neelshearer/beTheGoalie/GA/btg01.jpg

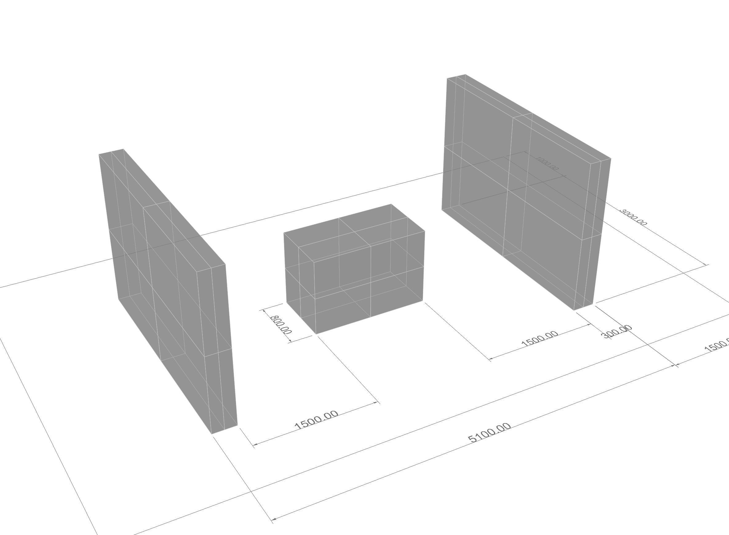
GA/btg01.jpg
