neelshearer/beTheGoalie/GA/btg02.jpg

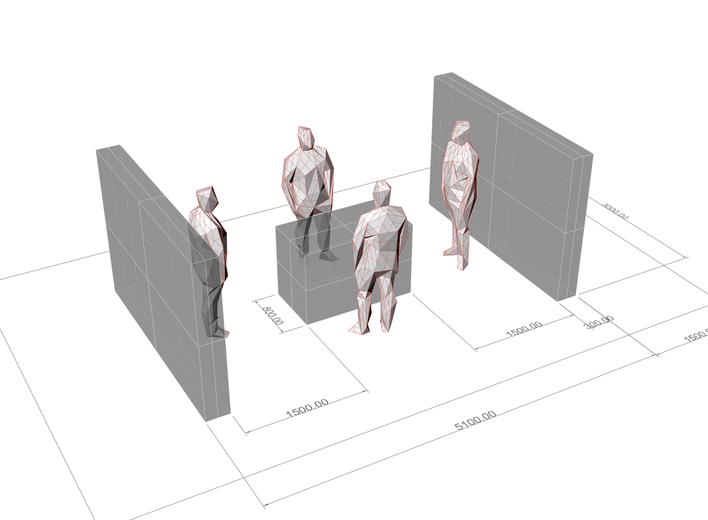
GA/btg02.jpg
