neelshearer/beTheGoalie/GA/btg03.jpg

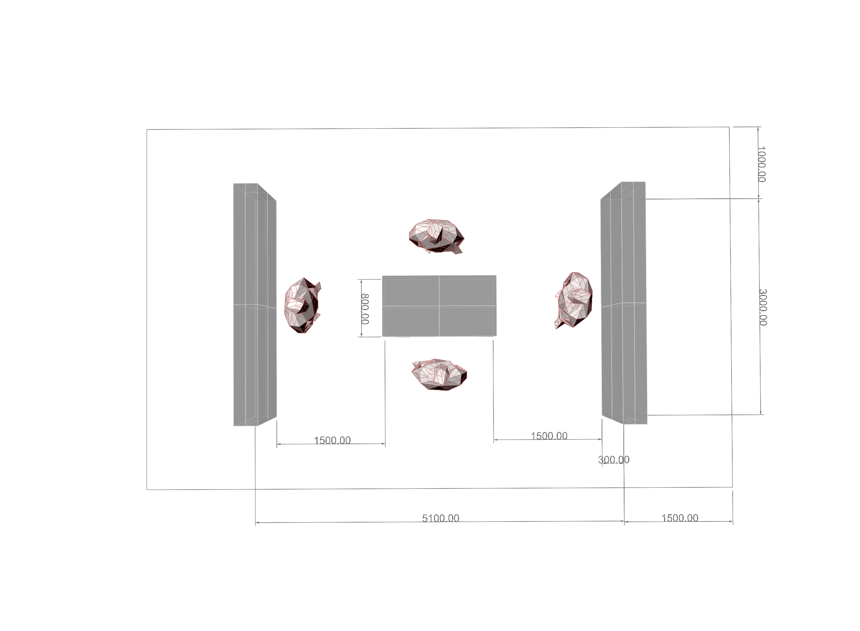
GA/btg03.jpg
