neelshearer/beTheGoalie/GA/btg04.jpg

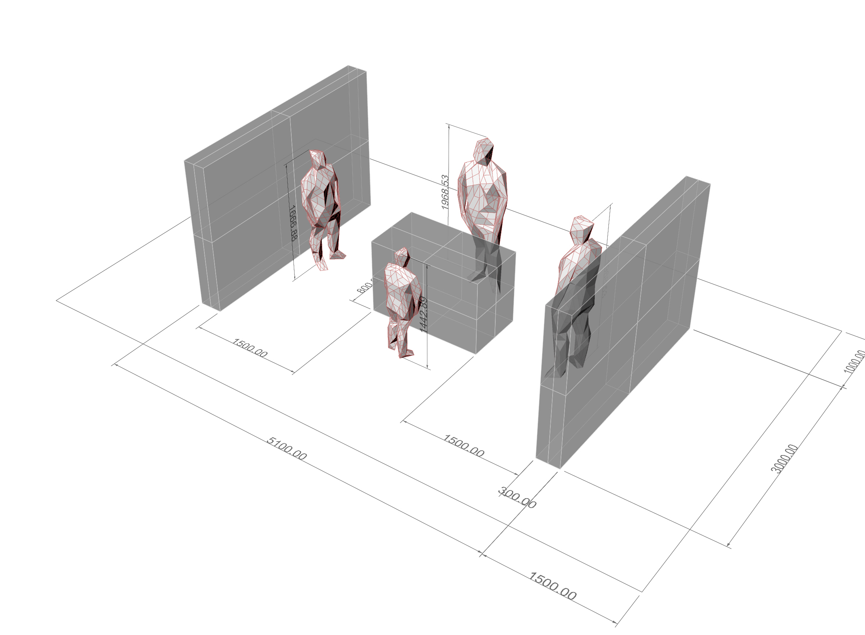
GA/btg04.jpg
