neelshearer/beTheGoalie/GA/btg06.jpg

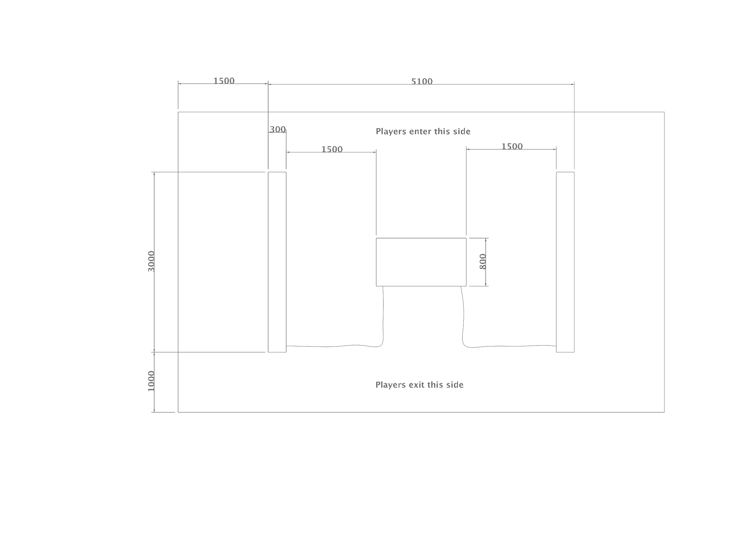
GA/btg06.jpg
