neelshearer/beTheGoalie/GA/btg07.jpg

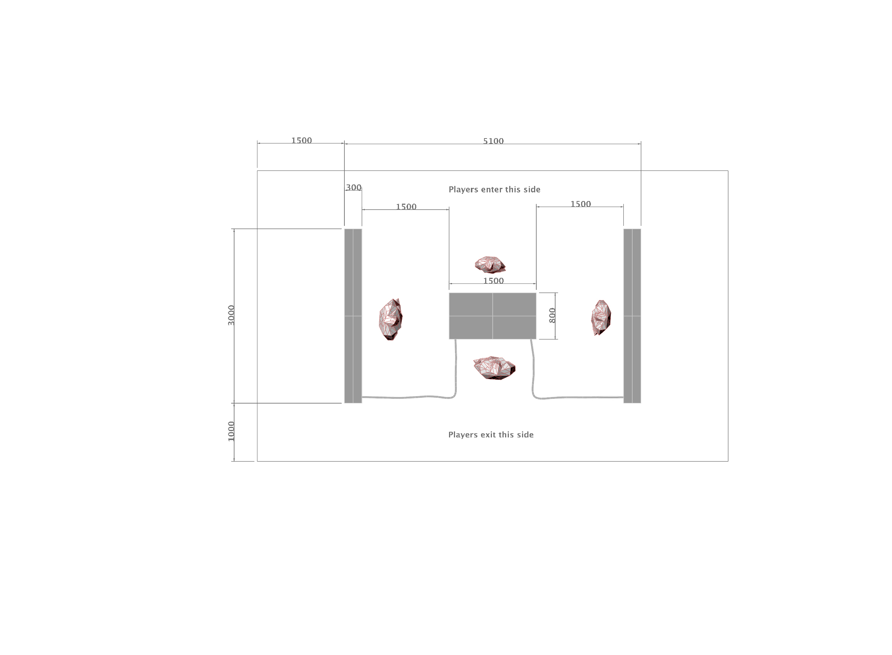
GA/btg07.jpg
