neelshearer/beTheGoalie/GA/btg10.jpg

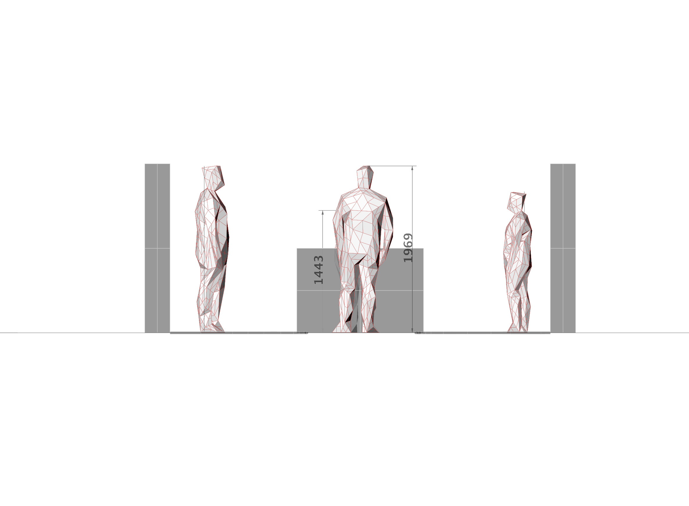
GA/btg10.jpg
