neelshearer/beTheGoalie/GA/btg12.jpg

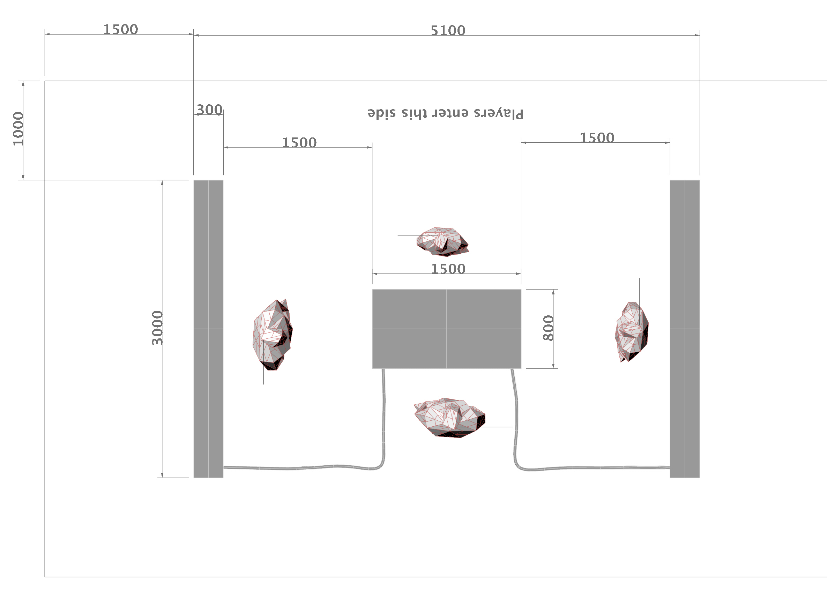
GA/btg12.jpg
