neelshearer/beTheGoalie/GA/btg13.jpg

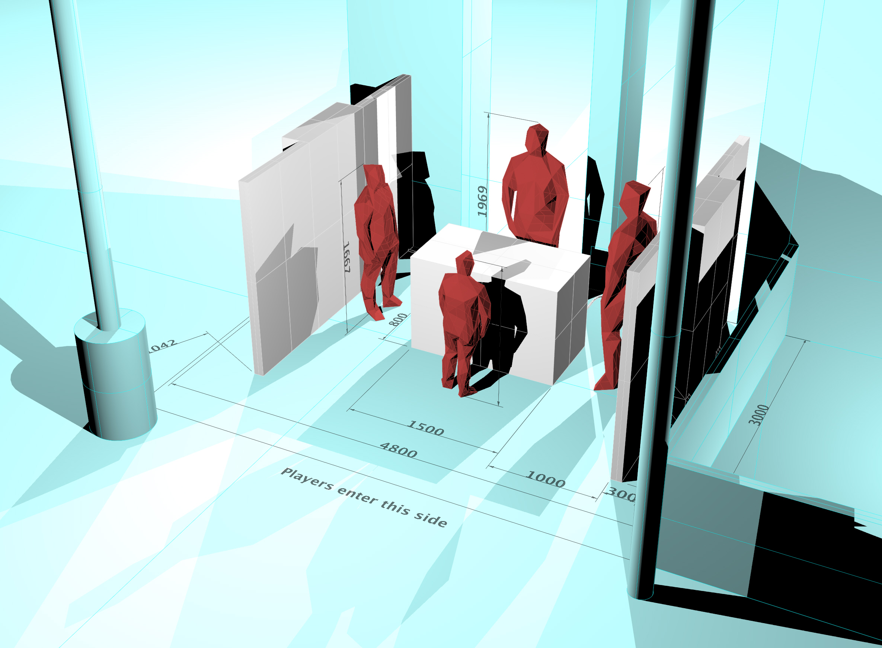
GA/btg13.jpg
