neelshearer/beTheGoalie/GA/my-friend-boris-1.snapshot.3/boris_lowpoly_160713.jpg

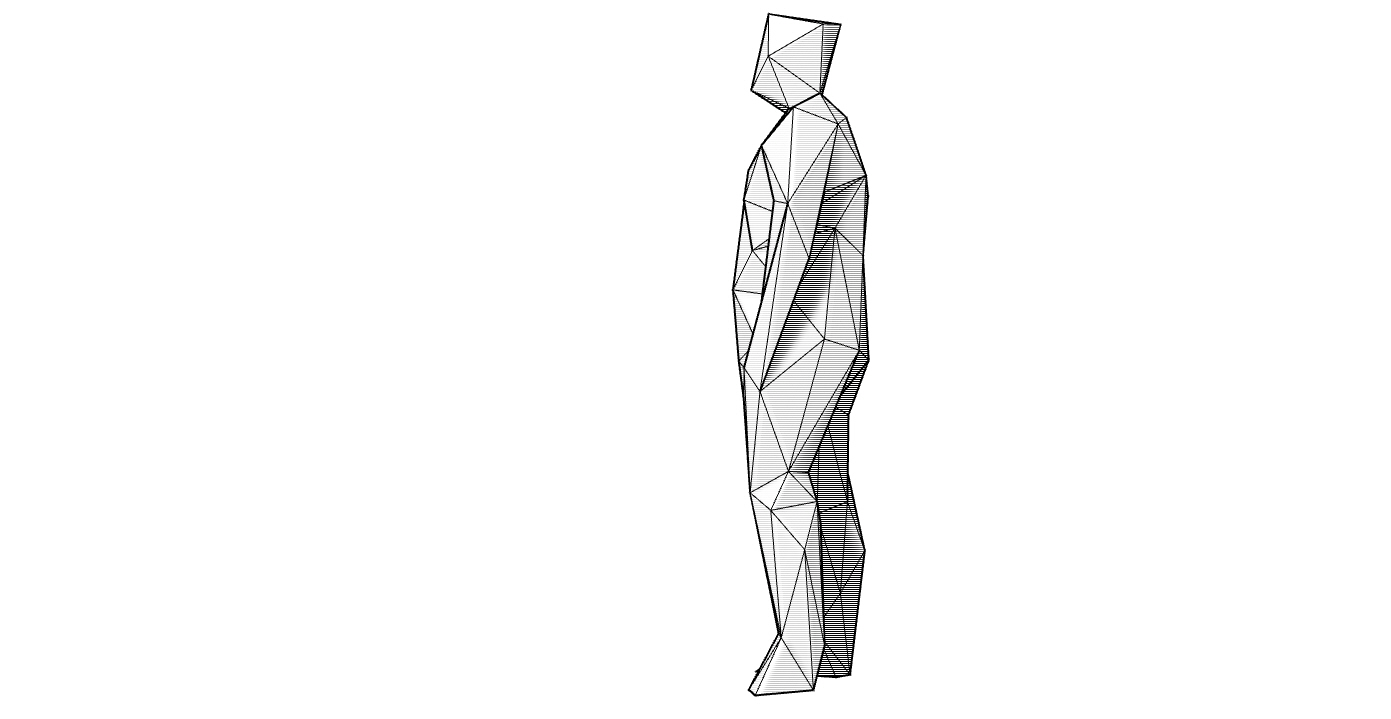
GA/my-friend-boris-1.snapshot.3/boris_lowpoly_160713.jpg
