neelshearer/beTheGoalie/Processing/BtG_mk25/data/photo4.jpg

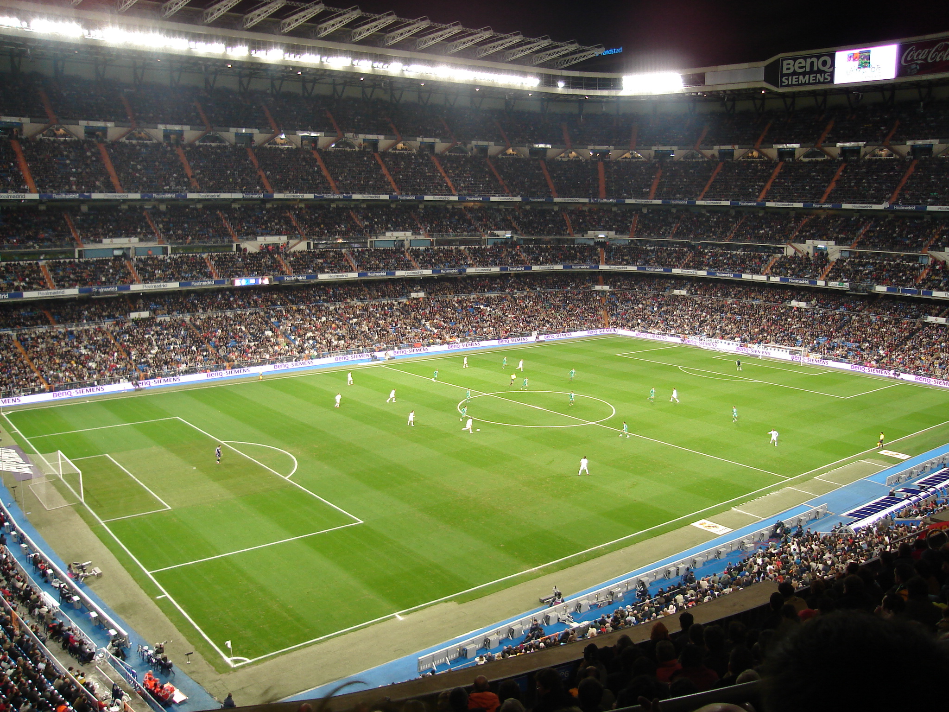
Processing/BtG_mk25/data/photo4.jpg
