neelshearer/beTheGoalie/wall structure mk2/Computer cavity and apertures.jpg

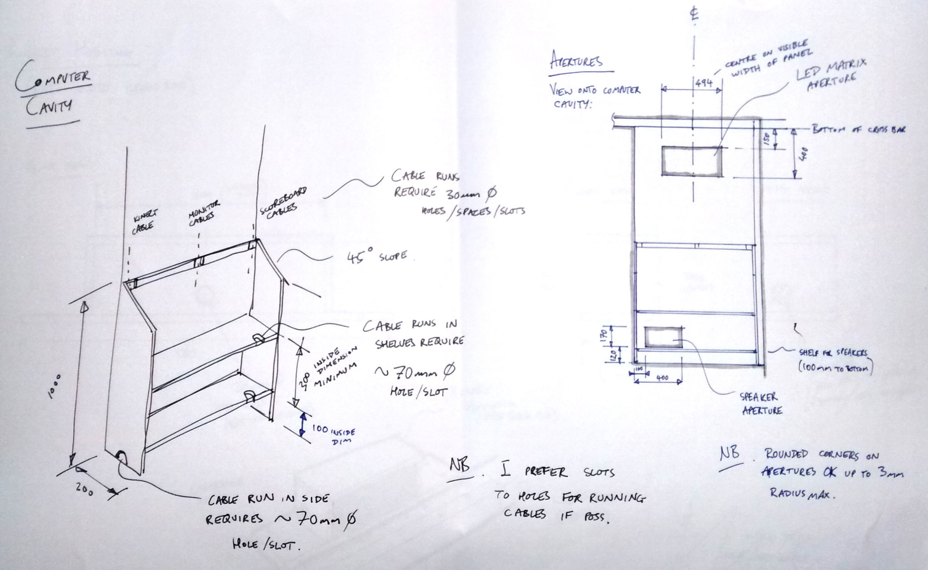
wall structure mk2/Computer cavity and apertures.jpg
