neelshearer/beTheGoalie/wall structure mk2/computer_cavity.jpg

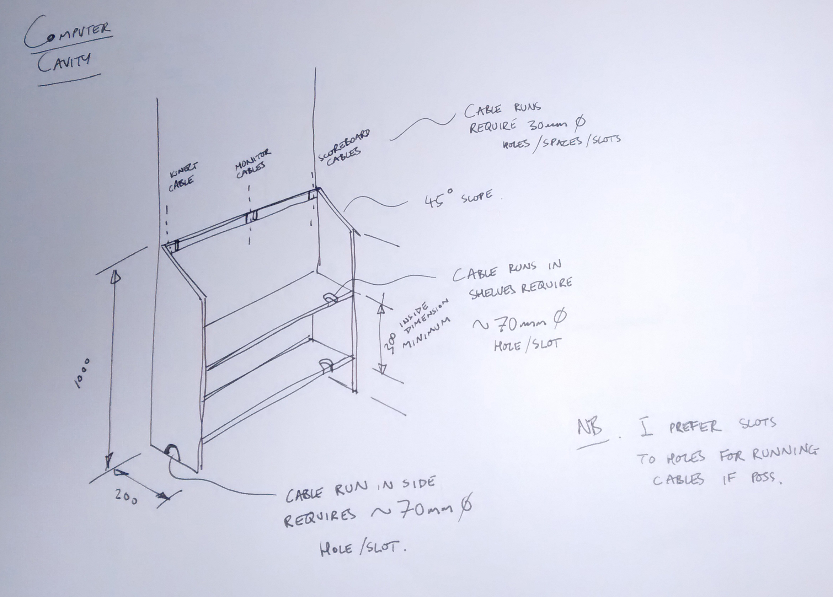
wall structure mk2/computer_cavity.jpg
