neelshearer/beTheGoalie/wall structure mk2/crossbar.jpg

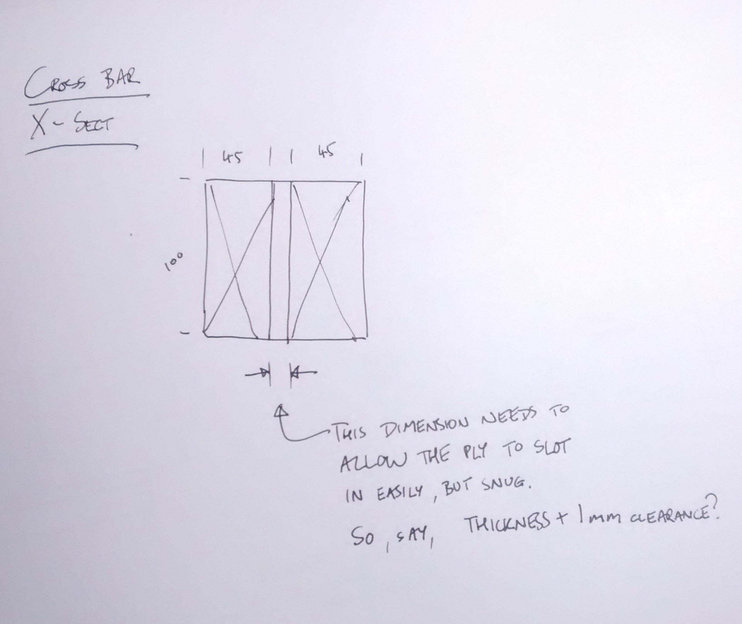
wall structure mk2/crossbar.jpg
