neelshearer/beTheGoalie/wall structure mk2/p1.jpg

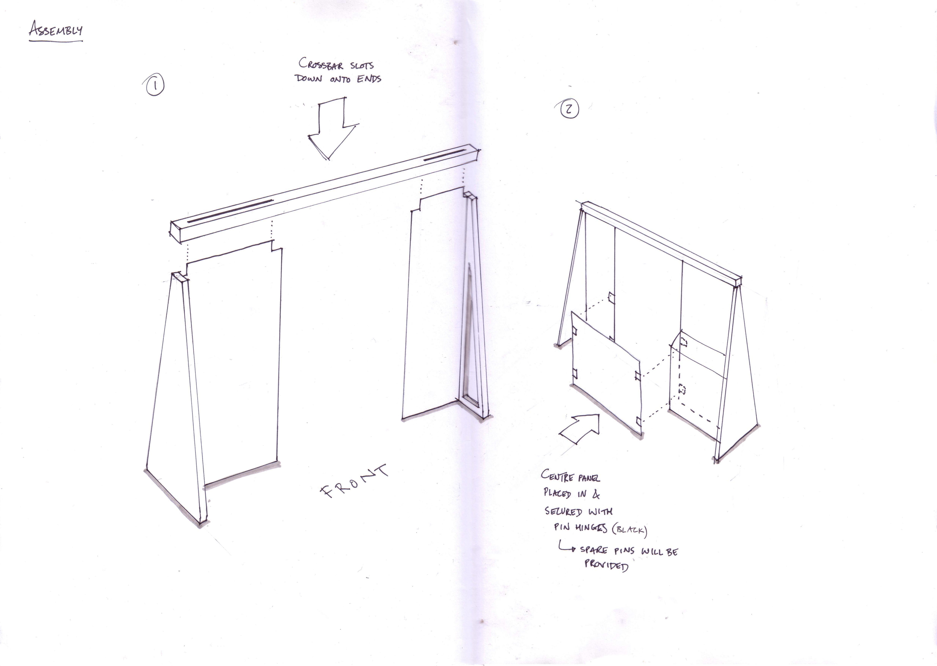
wall structure mk2/p1.jpg
