neelshearer/beTheGoalie/wall structure mk2/p2.jpg

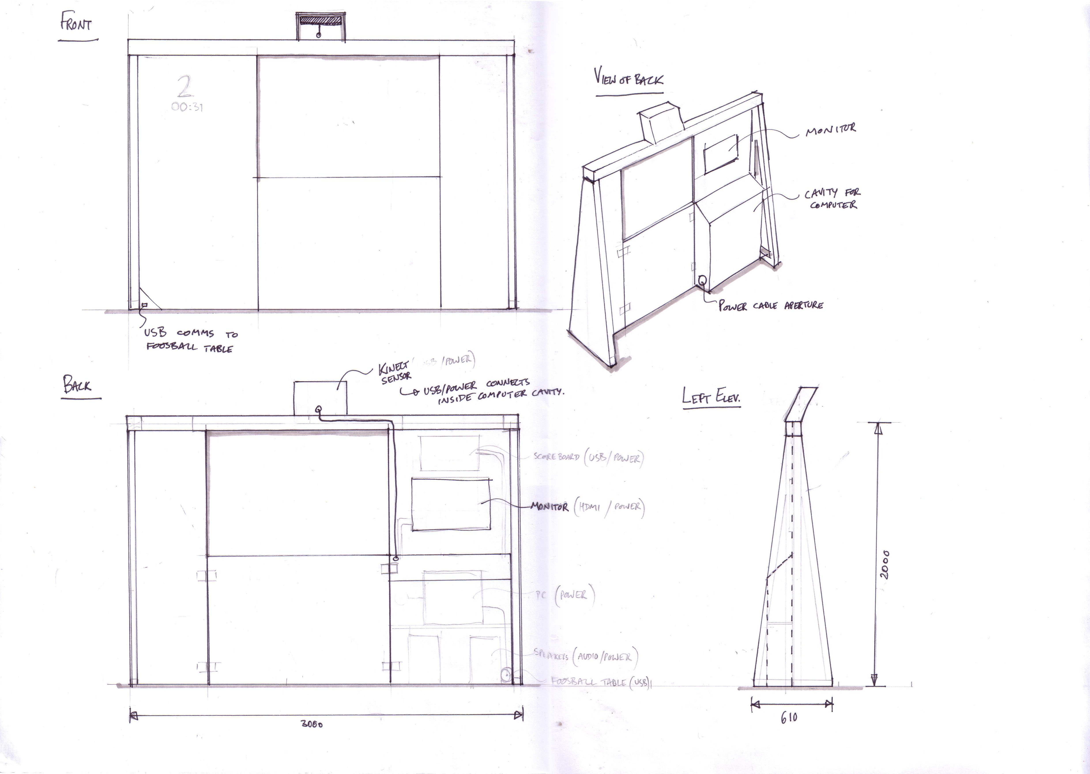
wall structure mk2/p2.jpg
