neelshearer/beTheGoalie/wall structure mk2/p3.jpg

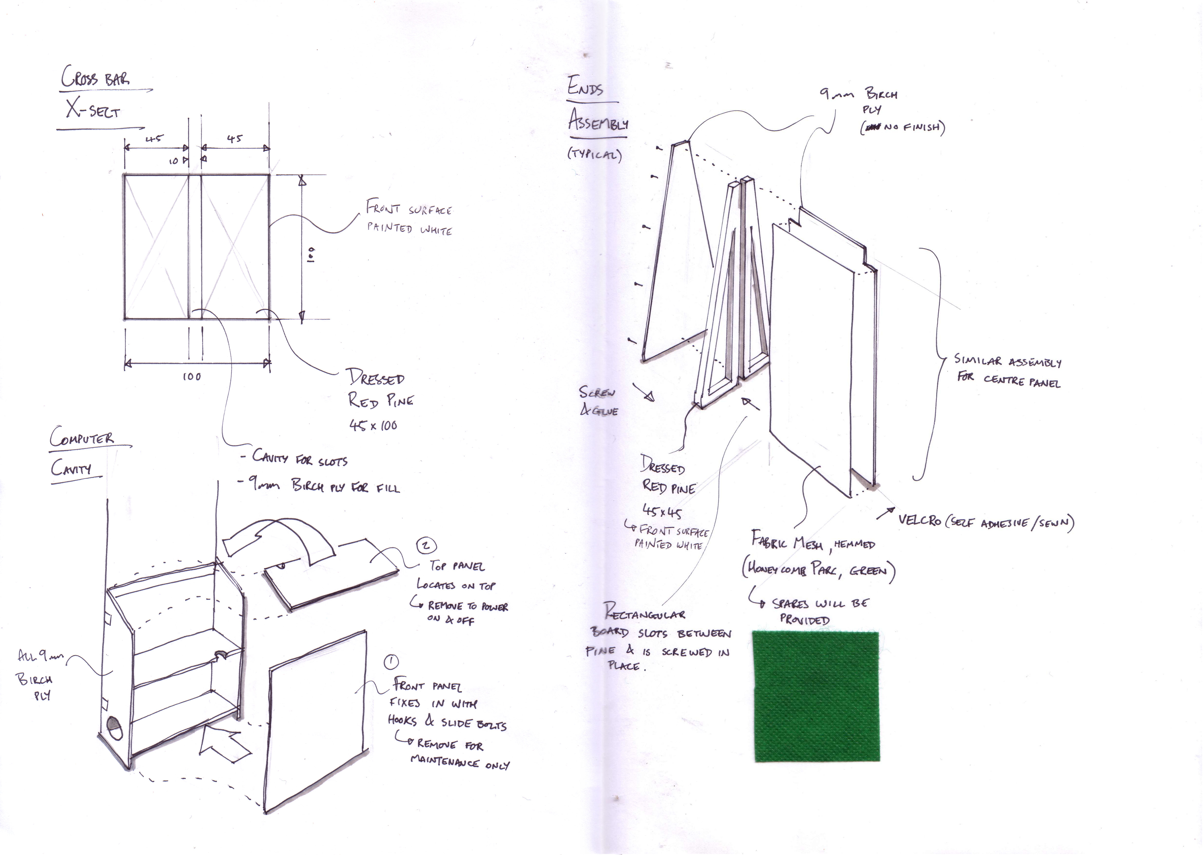
wall structure mk2/p3.jpg
