neelshearer/beTheGoalie/wall structure mk2/wall graphics/superceded/wall graphics-02.png

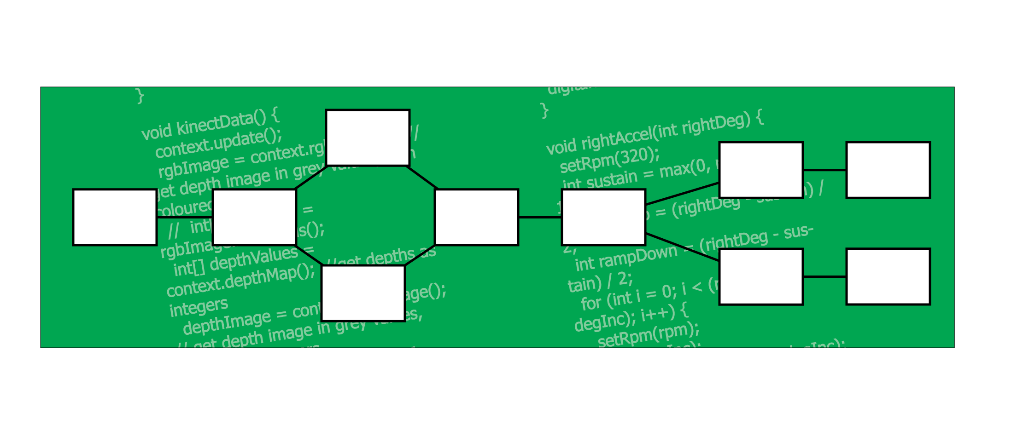
wall structure mk2/wall graphics/superceded/wall graphics-02.png
