neelshearer/beTheGoalie/wall structure mk2/wall graphics/superceded/wall graphics-03.png

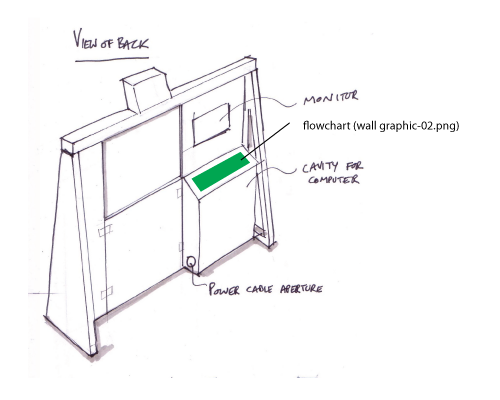
wall structure mk2/wall graphics/superceded/wall graphics-03.png
