neelshearer/beTheGoalie/wall structure mk2/wall graphics/superceded/wall graphics_RevA-01.png

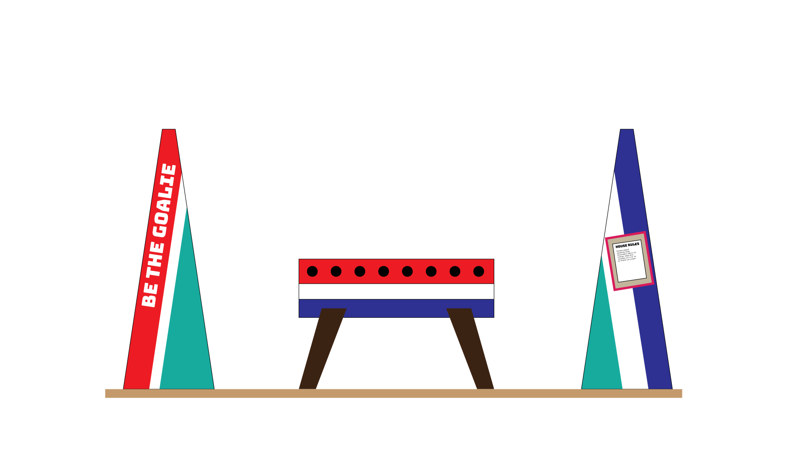
wall structure mk2/wall graphics/superceded/wall graphics_RevA-01.png
