neelshearer/beTheGoalie/wall structure mk2/wall graphics/superceded/wall graphics_RevA-02.png

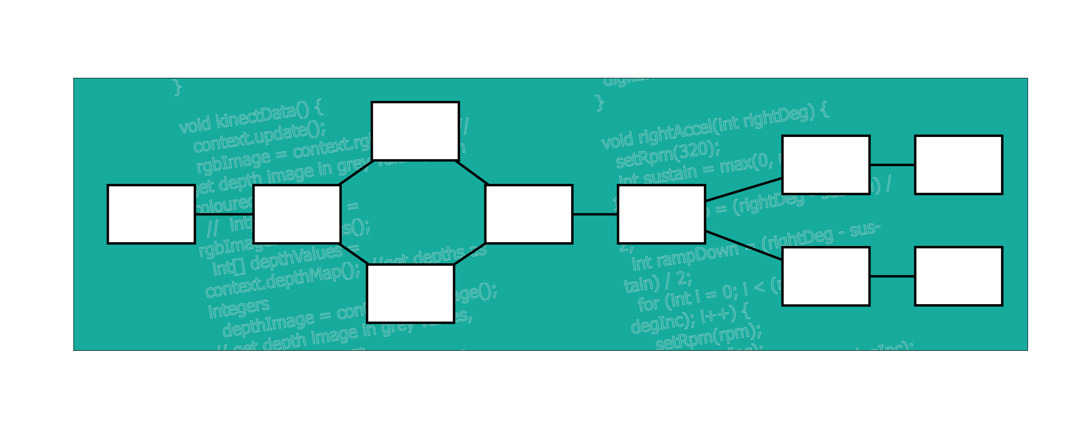
wall structure mk2/wall graphics/superceded/wall graphics_RevA-02.png
