neelshearer/beTheGoalie/wall structure mk2/wall graphics/wall graphics RevB-02.png

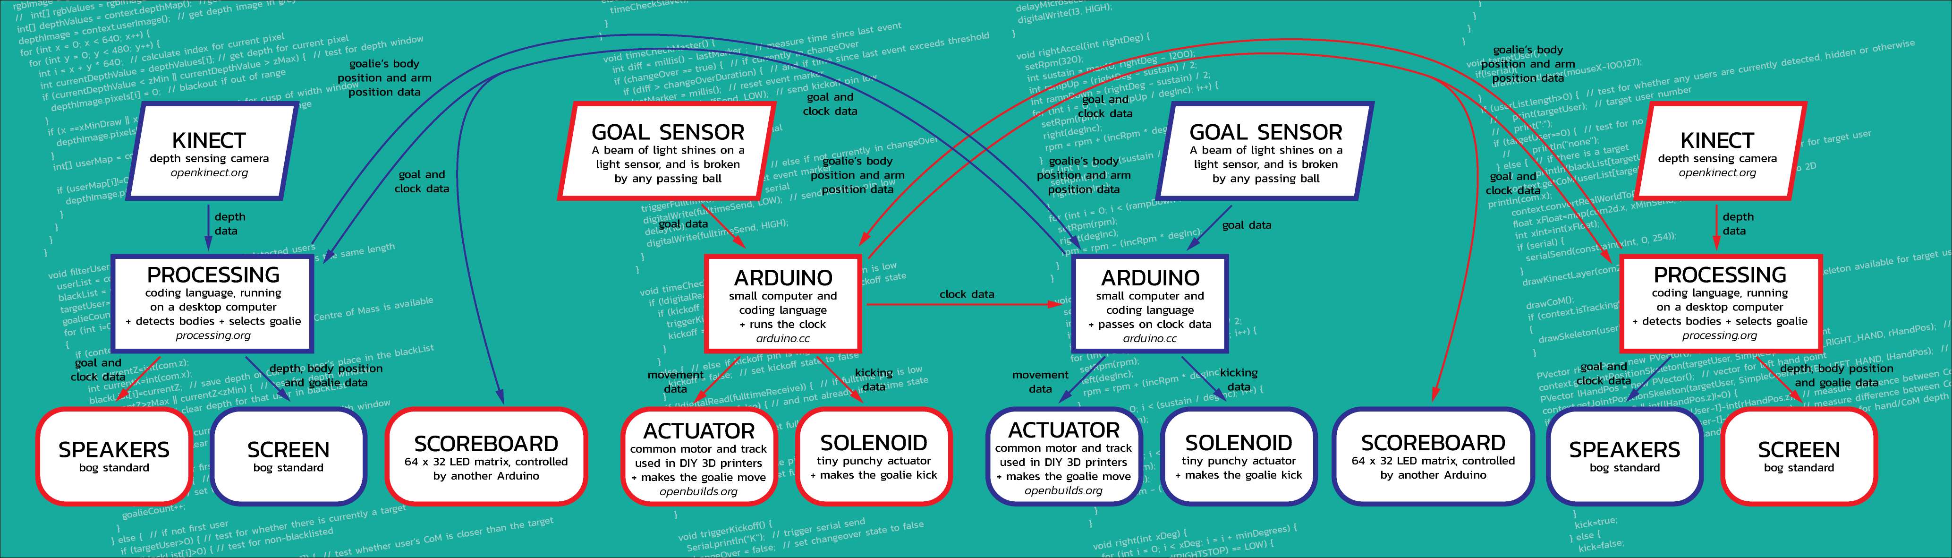
wall structure mk2/wall graphics/wall graphics RevB-02.png
