neelshearer/beTheGoalie/Arduino/arduinoBtG_mk10/SerialIn.ino

void serialSetup() {
  // start serial port at 9600 bps and wait for port to open:
  Serial.begin(115200);
  while (!Serial) {
    ; // wait for serial port to connect. Needed for native USB port only
  }
  establishContact();  // send a byte to establish contact until Processing responds 
}

void establishContact() {
 while (Serial.available() <= 0) {
      Serial.write('A');   // send a capital A
      delay(300);
  }
}

void serialLoop2() {
  // if we get a valid byte, read analog ins:
  if (Serial.available() > 0) {
    // get incoming byte:
    inByte = Serial.read();
    Serial.println(inByte);
  }
}
